Josue-Espinosa-Cruz/Baropodometry/1_PCB/2_CadModel/2_Components/2_OwnDesign/74HC595-shift/74HC595-shift-render.png

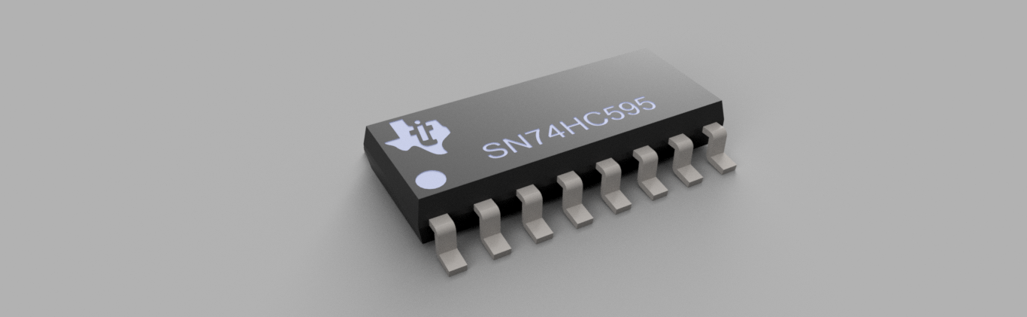
1_PCB/2_CadModel/2_Components/2_OwnDesign/74HC595-shift/74HC595-shift-render.png
