Josue-Espinosa-Cruz/Baropodometry/1_PCB/3_Images/1_Bottom/Bottom_Render.png

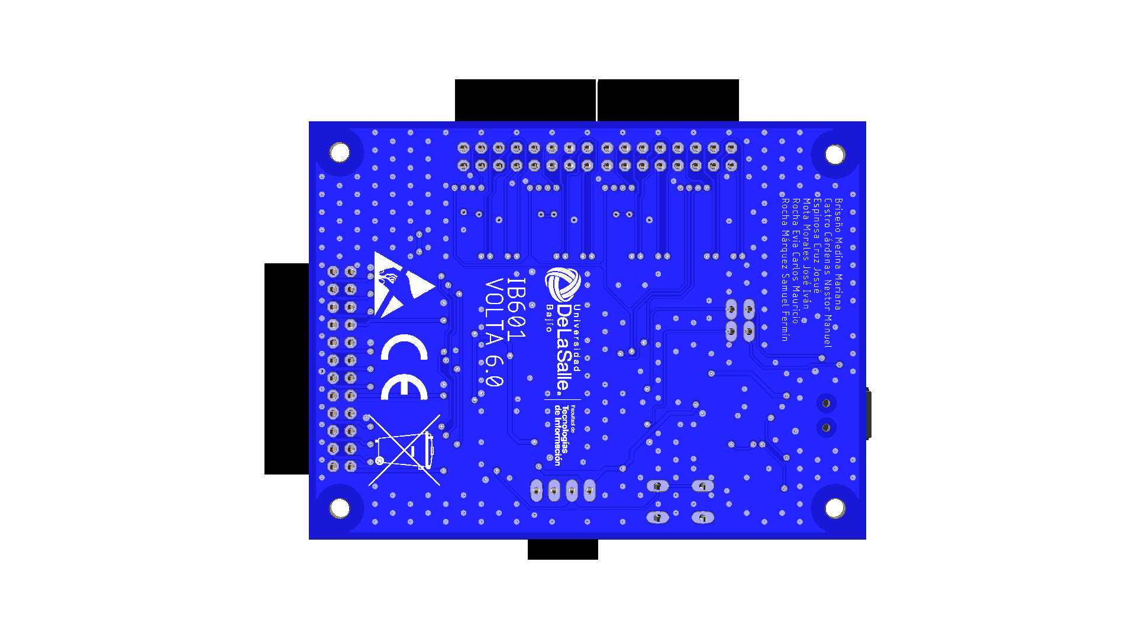
1_PCB/3_Images/1_Bottom/Bottom_Render.png
