Josue-Espinosa-Cruz/Baropodometry/1_PCB/3_Images/2_Top/Top_Eagle.png

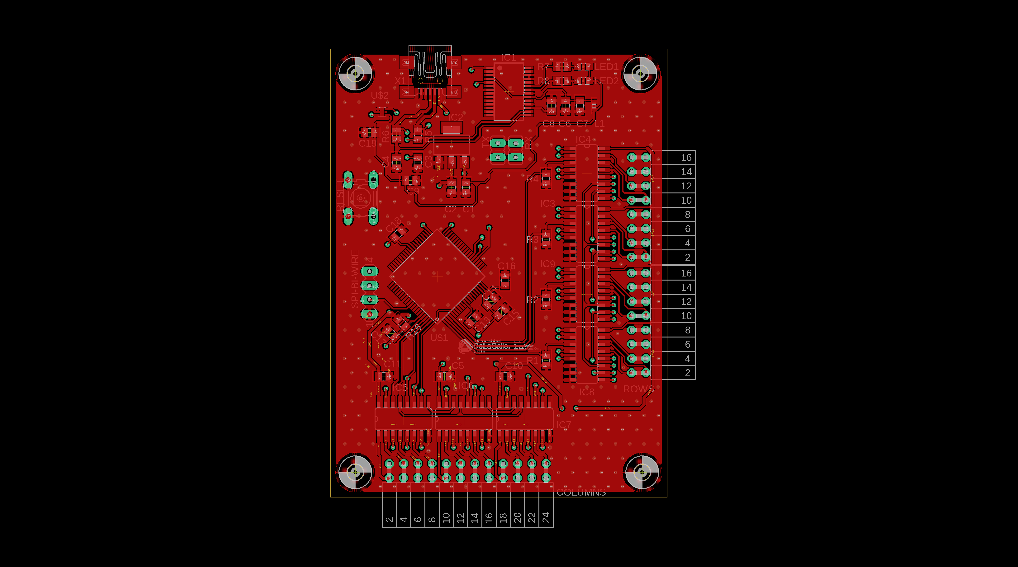
1_PCB/3_Images/2_Top/Top_Eagle.png
