Josue-Espinosa-Cruz/Baropodometry/1_PCB/3_Images/3_Drills/Baropodometer_Drills.png

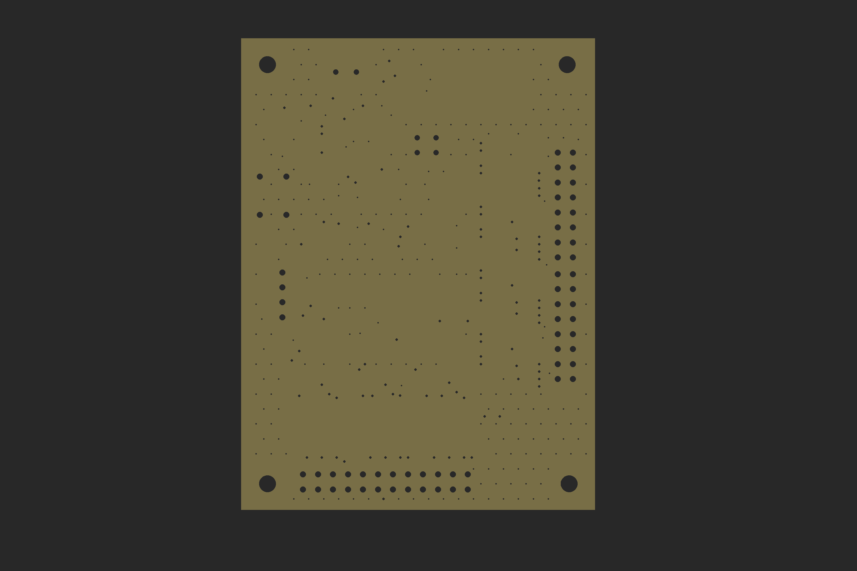
1_PCB/3_Images/3_Drills/Baropodometer_Drills.png
