Josue-Espinosa-Cruz/Baropodometry/1_PCB/2_CadModel/2_Components/1_GrabCAD/Female Headers By DL2DW - Dirk Wouters/1 Row Female Pin Header Pitch 2.54mm Height 8.5mm Right Angle/Female Pin Header 01x04 Right Angle.png

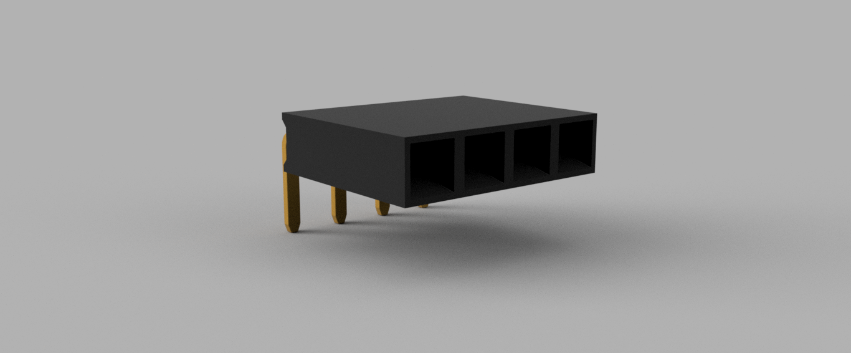
1_PCB/2_CadModel/2_Components/1_GrabCAD/Female Headers By DL2DW - Dirk Wouters/1 Row Female Pin Header Pitch 2.54mm Height 8.5mm Right Angle/Female Pin Header 01x04 Right Angle.png
