Josue-Espinosa-Cruz/Baropodometry/1_PCB/2_CadModel/2_Components/1_GrabCAD/Jumpler By DL2DW - Dirk Wouters/Jumper Closed.png

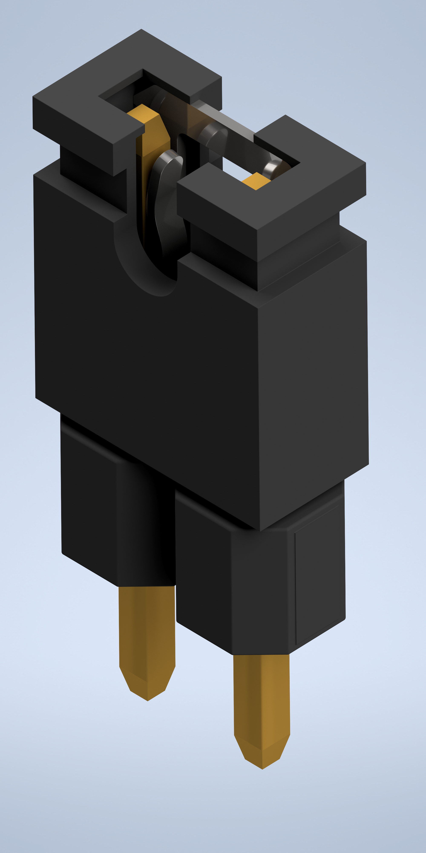
1_PCB/2_CadModel/2_Components/1_GrabCAD/Jumpler By DL2DW - Dirk Wouters/Jumper Closed.png
