Josue-Espinosa-Cruz/Baropodometry/1_PCB/2_CadModel/2_Components/1_GrabCAD/Male Headers - Vahagn Zargaryan/4x_Male_Pin_2.54_mm.png

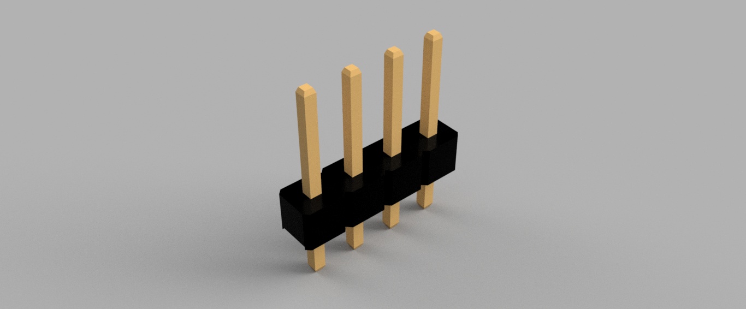
1_PCB/2_CadModel/2_Components/1_GrabCAD/Male Headers - Vahagn Zargaryan/4x_Male_Pin_2.54_mm.png
