Josue-Espinosa-Cruz/Baropodometry/1_PCB/2_CadModel/2_Components/1_GrabCAD/Mini USB/USB_MINI_B_SMD v35.png

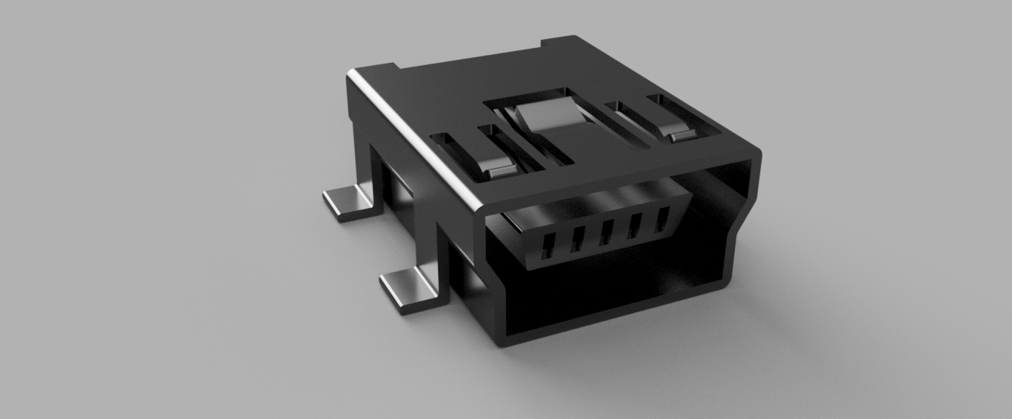
1_PCB/2_CadModel/2_Components/1_GrabCAD/Mini USB/USB_MINI_B_SMD v35.png
