Josue-Espinosa-Cruz/Baropodometry/1_PCB/3_Images/2_Top/Top_Manufacturing.png

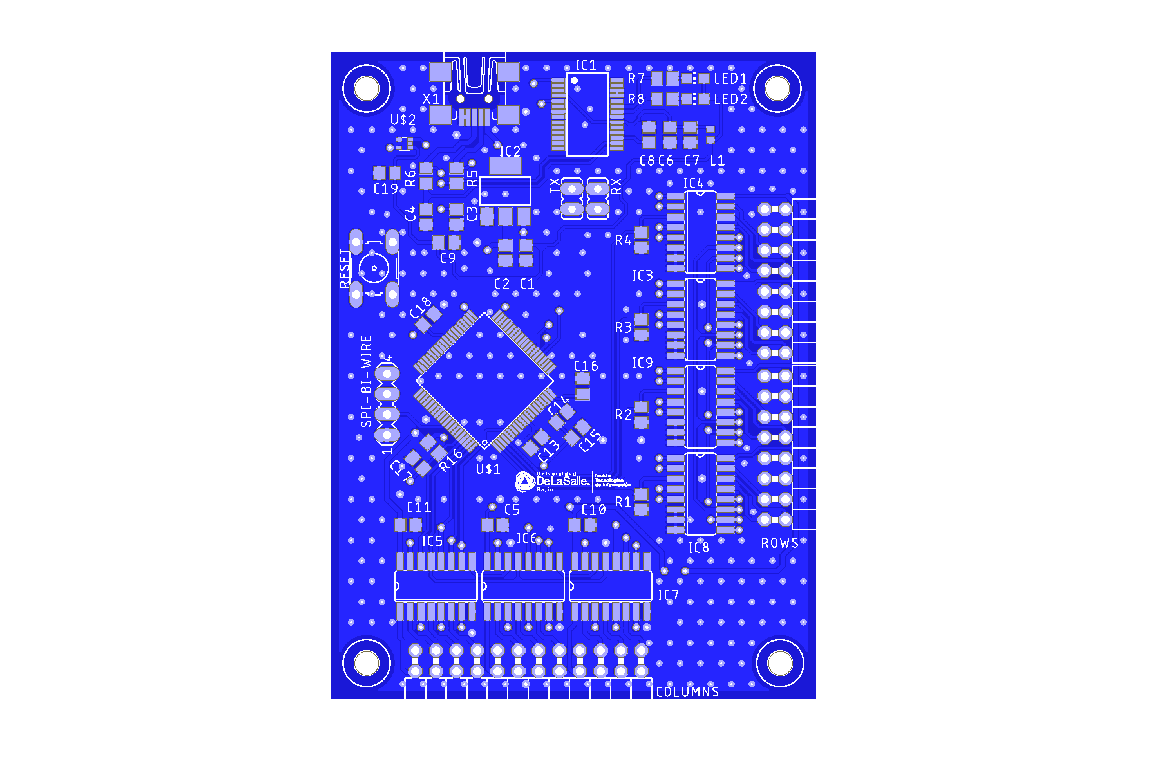
1_PCB/3_Images/2_Top/Top_Manufacturing.png
